afternoon/microgroove/hardware/microgroove.kicad_sch

## KiCad design hardware/microgroove.kicad_sch (2024-04-03, an earlier design)

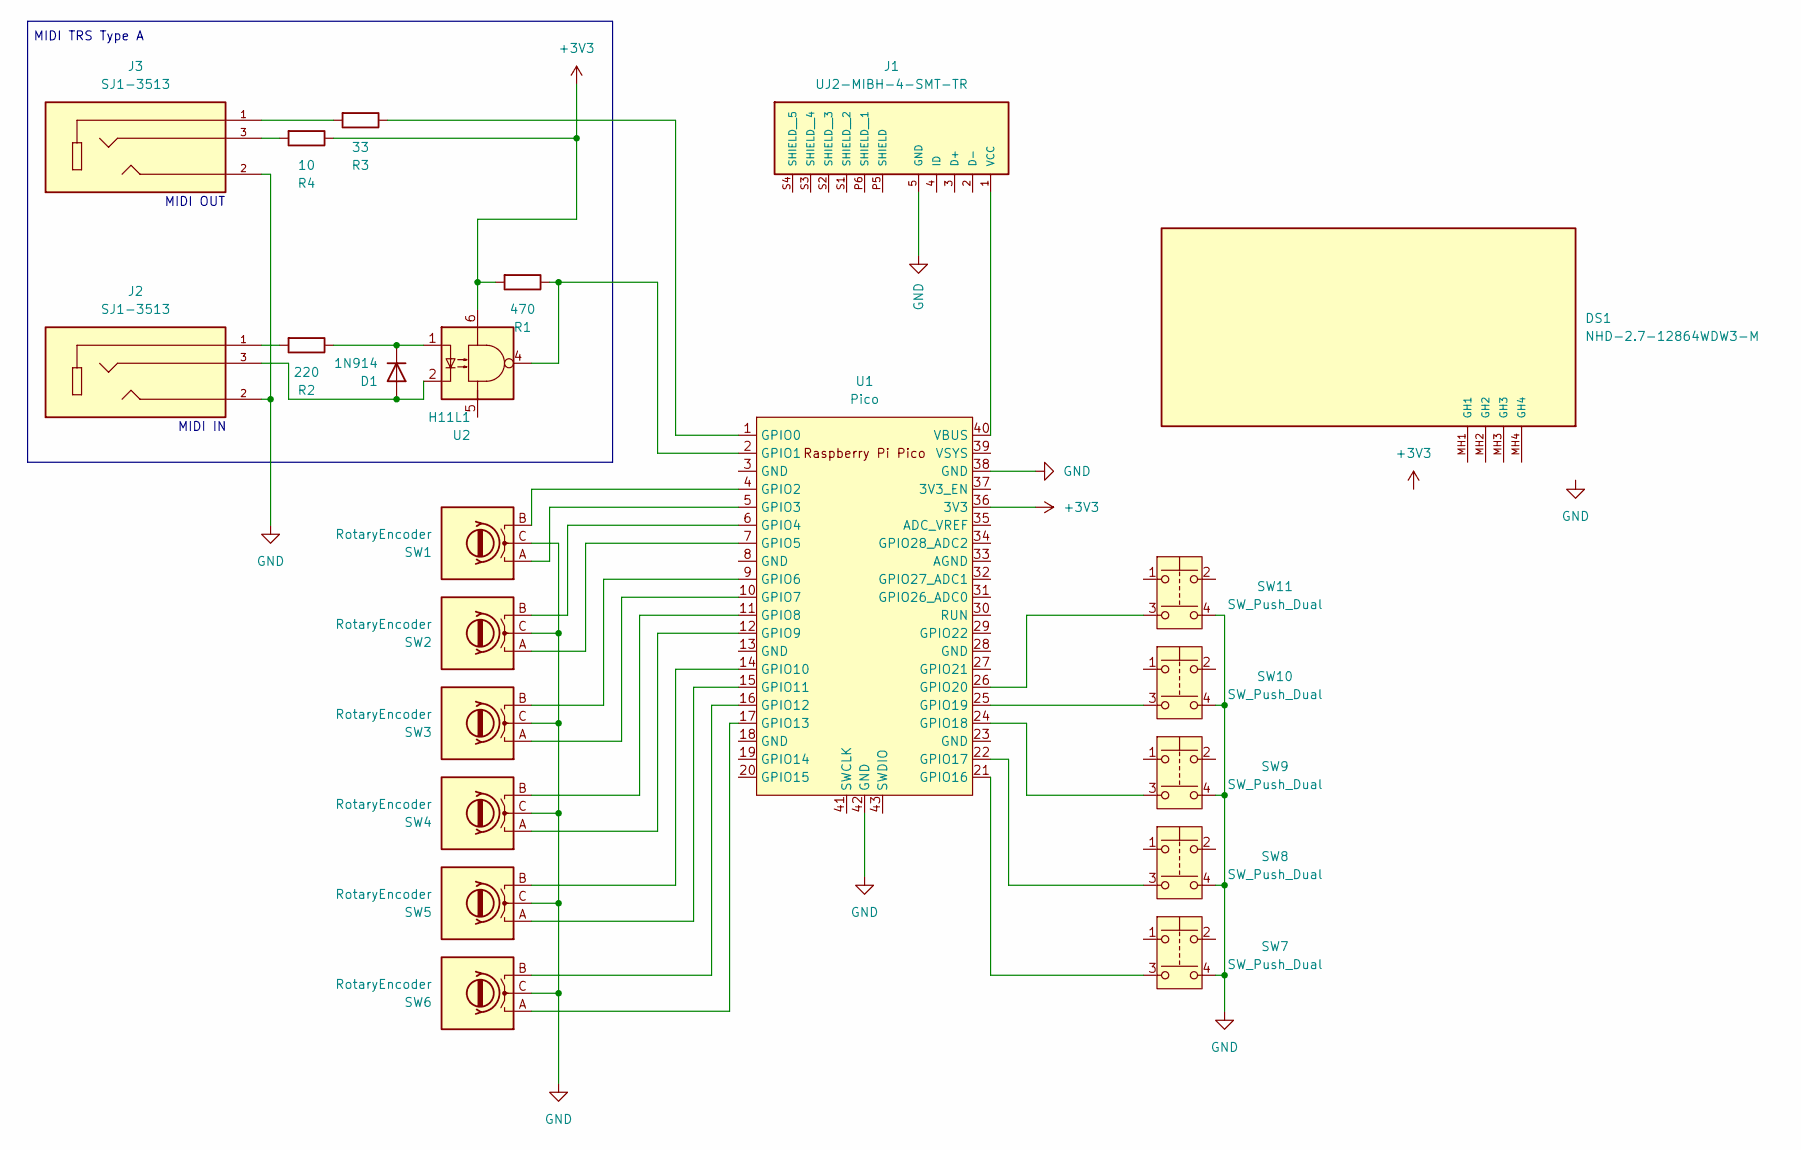
[picture p3: schematic microgroove.kicad_sch]

Parts:
D1: 1N914; D_DO-35_SOD27_P7.62mm_Horizontal
DS1: NHD-2.7-12864WDW3-M; NHD2712864WDW3-M; MOUSER_PART_NUMBER 763-NHD2712864WDW3
J1: UJ2-MIBH-4-SMT-TR; CUIDEVICES_UJ2-MIBH-4-SMT-TR
J2, J3: SJ1-3513; CUI_SJ1-3513; PARTREV 1.03
R1: 470
R2: 220
R3: 33
R4: 10
SW1, SW2, SW3, SW4, SW5, SW6: RotaryEncoder
SW7, SW8, SW9, SW10, SW11: SW_Push_Dual
U1: Pico; RPi_Pico_SMD_TH
U2: H11L1

Connections:
+3V3: R1.2, R4.1, U1.36 (3V3), U2.6
GND: J1.5 (GND), J2.2, J3.2, SW1.C, SW2.C, SW3.C, SW4.C, SW5.C, SW6.C, SW7.4, SW8.4, SW9.4, SW10.4, SW11.4, U1.38 (GND), U1.42 (GND)
unnamed: D1.1 (K), R2.1, U2.1
unnamed: D1.2 (A), J2.3, U2.2
unnamed: J1.1 (VCC), U1.40 (VBUS)
unnamed: J2.1, R2.2
unnamed: J3.1, R3.2
unnamed: J3.3, R4.2
unnamed: R1.1, U1.2 (GPIO1), U2.4
unnamed: R3.1, U1.1 (GPIO0)
unnamed: SW1.A, U1.5 (GPIO3)
unnamed: SW1.B, U1.4 (GPIO2)
unnamed: SW2.A, U1.7 (GPIO5)
unnamed: SW2.B, U1.6 (GPIO4)
unnamed: SW3.A, U1.10 (GPIO7)
unnamed: SW3.B, U1.9 (GPIO6)
unnamed: SW4.A, U1.12 (GPIO9)
unnamed: SW4.B, U1.11 (GPIO8)
unnamed: SW5.A, U1.15 (GPIO11)
unnamed: SW5.B, U1.14 (GPIO10)
unnamed: SW6.A, U1.17 (GPIO13)
unnamed: SW6.B, U1.16 (GPIO12)
unnamed: SW7.3, U1.21 (GPIO16)
unnamed: SW8.3, U1.22 (GPIO17)
unnamed: SW9.3, U1.24 (GPIO18)
unnamed: SW10.3, U1.25 (GPIO19)
unnamed: SW11.3, U1.26 (GPIO20)

Notes on the sheet:
MIDI TRS Type A
MIDI IN
MIDI OUT
